MOSH-Insa-Toulouse/5ISS-Gautheron-Lagrost/_LTSpice/GasSensor.asc

B1: bi; I=V(cp,cn)*({G0}+(V(gc,gn)*{G1}))
C1: cap; 200µ
R1: res; 1k
Named nets: gp, gn, cp, cn, gc
