MOSH-Insa-Toulouse/5ISS-Gautheron-Lagrost/_LTSpice/TransimpedanceAmpStage.asc

C1: cap; 1p
C2: cap; 100n
C3: cap; 1µ
C4: cap; 100n
R1: res; 10k
R2: res; {R2}
R3: res; 1k
R4: res; 100k
R5: res; 1k
U1: LTC1050
V1: voltage; PULSE(0 1 0.2 0.1 0.1 20)
V2: voltage; SINE(0 325 50)
V3: voltage; 5
X1: GasSensor
Named nets: 0, ADC
.tran 2
.param R2=300k G0=10n G1=10n
