MOSH-Insa-Toulouse/5ISS-Gautheron-Lagrost/_LTSpice/ConductivityGenerator.asc

C1: cap; 10µ
R1: res; 10k
V1: voltage; PULSE(0 5 0 0 0 1 3)
Named nets: 0
.tran 10
